scottlbaker/usdx644/firmware/include/user.h

//==========================================================
//  user.h ::  user variables
//==========================================================

#define MAXSTR 10

char mycall[MAXSTR] = "KJ7NLA";
char myname[MAXSTR] = "SCOTT";
char  myant[MAXSTR] = "EFHW";
char  myrig[MAXSTR] = "USDX";
char  mypwr[MAXSTR] = "5W";
char  myqth[MAXSTR] = "OR";
